SchmidtBytes/StopLight/programs/StopLight_3_WiFi/wifi_favicons.h

#ifndef STOP_LIGHT_WIFI_FAVICONS_H
#define STOP_LIGHT_WIFI_FAVICONS_H

#include "WString.h"
#include "state_enum.h"

const String favicon_f = "data:image/png;base64,iVBORw0KGgoAAAANSUhEUgAAADAAAAAwCAYAAABXAvmHAAABg2lDQ1BJQ0MgcHJvZmlsZQAAKJF9kT1Iw0AcxV9btVIqDnaQ4pChOlkoKuKoVShChVArt"
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
const String favicon_p = "data:image/png;base64,iVBORw0KGgoAAAANSUhEUgAAADAAAAAwCAYAAABXAvmHAAABg2lDQ1BJQ0MgcHJvZmlsZQAAKJF9kT1Iw0AcxV9btVIqDnaQ4pChOlkoKuKoVShChVArt"
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
const String favicon_s = "data:image/png;base64,iVBORw0KGgoAAAANSUhEUgAAADAAAAAwCAYAAABXAvmHAAABg2lDQ1BJQ0MgcHJvZmlsZQAAKJF9kT1Iw0AcxV9btVIqDnaQ4pChOlkoKuKoVShChVArt"
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
const String favicon_u = "data:image/png;base64,iVBORw0KGgoAAAANSUhEUgAAADAAAAAwCAYAAABXAvmHAAABg2lDQ1BJQ0MgcHJvZmlsZQAAKJF9kT1Iw0AcxV9btVIqDnaQ4pChOlkoKuKoVShChVArt"
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
const String favicon_i = "data:image/gif;base64,R0lGODlhMAAwAIQVAAAAABAQEBUVFRoaGncAAB4eHh8fH44AAKQAALkAALwAAAGIBAKhBQK6B6CODwPRCgPVCr2pFNrDGfXbHfnfHhQUFBQUFBQUFBQUF"
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
const String favicon_o = "data:image/png;base64,iVBORw0KGgoAAAANSUhEUgAAADAAAAAwCAYAAABXAvmHAAABg2lDQ1BJQ0MgcHJvZmlsZQAAKJF9kT1Iw0AcxV9btVIqDnaQ4pChOlkoKuKoVShChVArt"
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
const String favicon_n = "data:image/gif;base64,R0lGODlhMAAwAOMLAAAAABAQEBUVFRoaGh4eHh8fH6COD72pFNrDGfXbHfnfHhQUFBQUFBQUFBQUFBQUFCH/C05FVFNDQVBFMi4wAwEAAAAh+QQJMgAPA"
                         "CwAAAAAMAAwAAAE/vDJSau9OGsNuv/fJnJgGY7oZK5emrKsi5bBQBBDUMojKBTAoADEE30CwWRB1yqSOgNlcHByYj4EKZBQtVqw2gK36f16oloquUw5hpkdttnzUw678gfNhoOv8zAr"
                         "eW2BO4MShYaHiUSHeiAGCAkJCAaKgyAHCpucB42LHgacowqWf3IfCKScCHioHgmrmwmubB+xsrSnth6qsq27ZR+isqZxjpmrnrXCkJKUxsFejMzT1Meg146P2sggNTc5l4AfdUl30lZ"
                         "uWn7bH2hSatiYHllaY/PkHfZS+ADuZ8LI++etAxJ21dSVk4Iu36sjfMR9otctG7Vt3BJhRKRx48YIACH5BAEyAA8ALAAAAAAwADAAAATf8MlJq704aw26/98mcmAZjuhkrl6asqyLls"
                         "FAEENQyiMoFMCgAMQTfQLBZEHXKpI6A2VwcHJiPgQpkFC1WrDaArfp/XqiWiq5TDmGmR222fNTDrvyB82Gg6/zMCt5bYE7gxKFhoeJRId6IDU3OYqDPlJ3f3JuWn6Oj1BhanGOYFpjo"
                         "4seWaZ4mmehrWybUp2kH3VJmKiVkHyTjamMu4DCw67FnsXGsr2SfstllnbAvB1InLHRr2nZXqVSpwDJqmHh46DcmczWb91W0rnUxEe+z+K2yPjCnp+J/Ij+/v2LAAA7";
const String favicon_b = "data:image/gif;base64,R0lGODlhMAAwAKU4AAAAABAQEBUVFRoaGh4cEB4eHh8fHyYjFS0qGjQwHjcxEDUxH0I7FU5FEE5GGlhQHlpRH11TFWNYD21hGXVoD3ZpFHtuHn1wH4R2D"
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
const String favicon_w = "data:image/gif;base64,R0lGODlhMAAwAIQQAAAAABAQEBUVFRoaGncAAB4eHh8fH44AAKQAALkAALwAAAGIBAKhBQK6BwPRCgPVChQUFBQUFBQUFBQUFBQUFBQUFBQUFBQUFBQUF"
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
const String favicon_a = "data:image/gif;base64,R0lGODlhMAAwAIQVAAAAABAQEBUVFRoaGncAAB4eHh8fH44AAKQAALkAALwAAAGIBAKhBQK6B6CODwPRCgPVCr2pFNrDGfXbHfnfHhQUFBQUFBQUFBQUF"
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
const String favicon_r = "data:image/gif;base64,R0lGODlhMAAwAIQVAAAAABAQEBUVFRoaGncAAB4eHh8fH44AAKQAALkAALwAAAGIBAKhBQK6B6CODwPRCgPVCr2pFNrDGfXbHfnfHhQUFBQUFBQUFBQUF"
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
const String favicon_$ = "data:image/gif;base64,R0lGODlhMAAwAKUkAAAAABAQEBUVFUAMDBoaGncAAB4eHk0RER8fH44AAFkVFaQAALkAALwAAGYZGWcaGg1IDRFXElVMEBVlFmZbFRpzGhp1GwGIBHZqG"
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
const String favicon_c = "data:image/gif;base64,R0lGODlhMAAwAIQVAAAAABAQEBUVFRoaGncAAB4eHh8fH44AAKQAALkAALwAAAGIBAKhBQK6B6CODwPRCgPVCr2pFNrDGfXbHfnfHhQUFBQUFBQUFBQUF"
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

const String favicon_wtf = "data:image/png;base64,iVBORw0KGgoAAAANSUhEUgAAADAAAAAwCAYAAABXAvmHAAABg2lDQ1BJQ0MgcHJvZmlsZQAAKJF9kT1Iw0AcxV9btVIqDnaQ4pChOlkoKuKoVShChVArt"
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

String get_favicon(StopLightState state) {
    switch(state) {
        case STATE_FAILED:
            return favicon_f;
        case STATE_PREPARE:
            return favicon_p;
        case STATE_SUCCESS:
            return favicon_s;
        case STATE_UNSTABLE:
            return favicon_u;
        case STATE_INIT:
            return favicon_i;
        case STATE_OFF:
            return favicon_o;
        case STATE_NIGHT:
            return favicon_n;
        case STATE_BUILDING:
            return favicon_b;
        case STATE_WAIT:
            return favicon_w;
        case STATE_ALTERNATE:
            return favicon_a;
        case STATE_ROLLING:
            return favicon_r;
        case STATE_PARTY:
            return favicon_$;
        case STATE_CYCLE:
            return favicon_c;
        default:
            return favicon_wtf;
    }
}

#endif // STOP_LIGHT_WIFI_FAVICONS_H
